marwansallam88/Touch-Piano-screen-based-on-capacitance-transducers/Photos/Cap_Piano_PCB.png

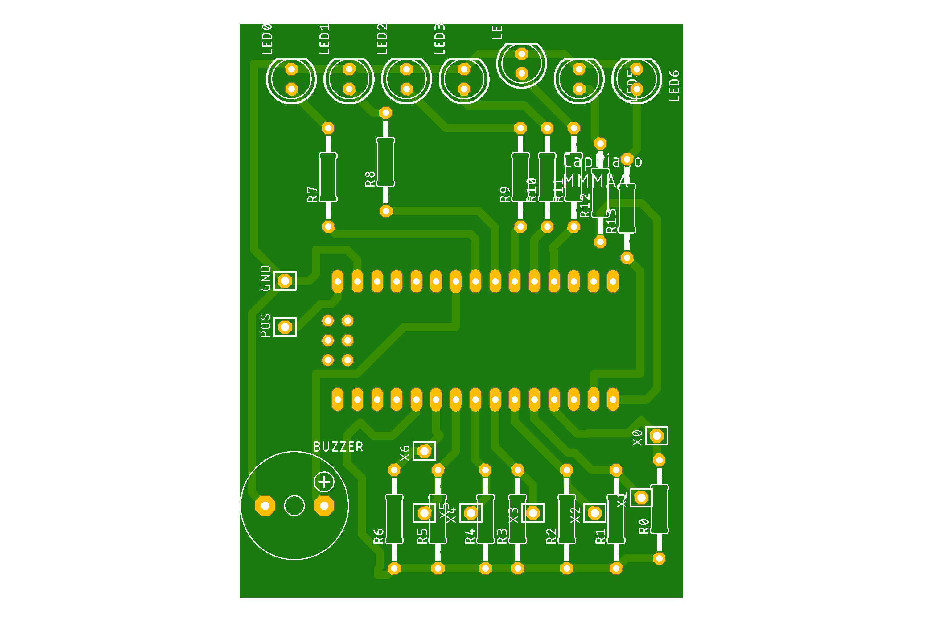
Photos/Cap_Piano_PCB.png
