marwansallam88/Touch-Piano-screen-based-on-capacitance-transducers/Report/Setup.jpg

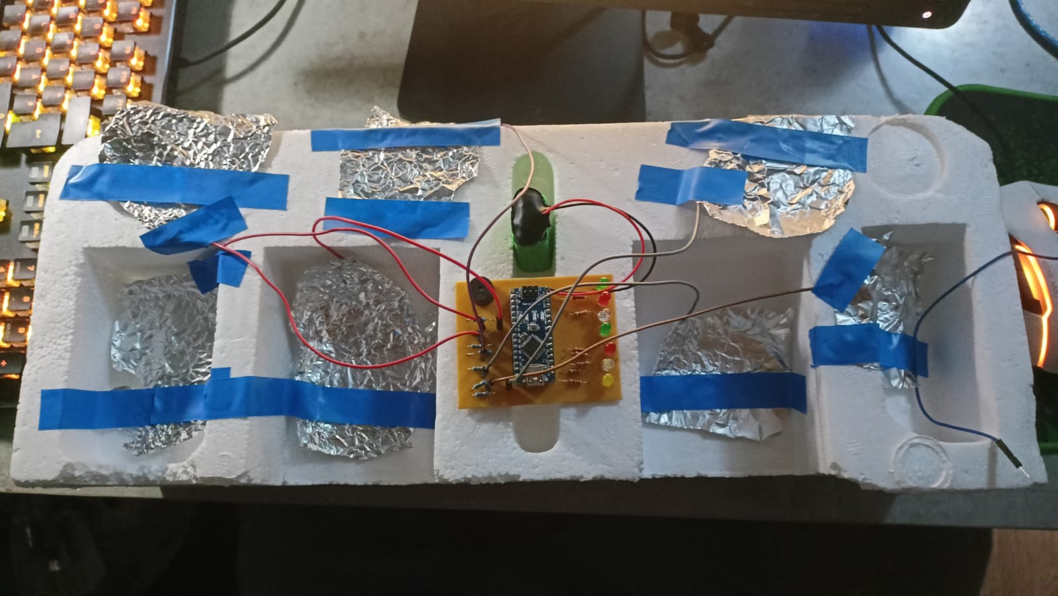
Report/Setup.jpg
